bazauto/block-detection/enclosure/previews/asm_bottom.png

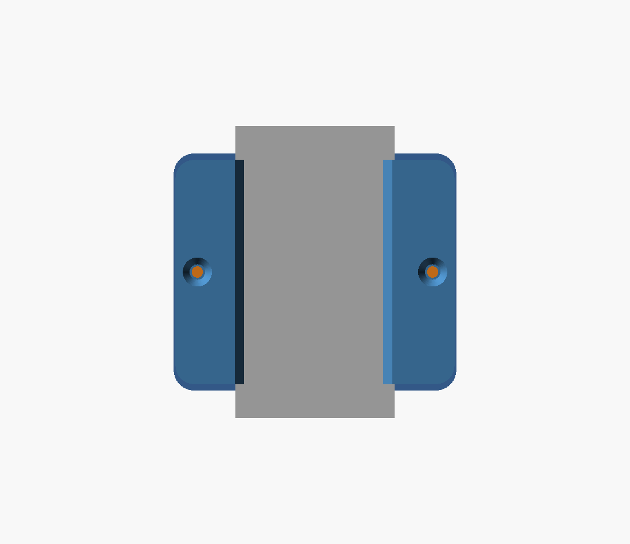
enclosure/previews/asm_bottom.png
