bazauto/block-detection/enclosure/previews/asm_front.png

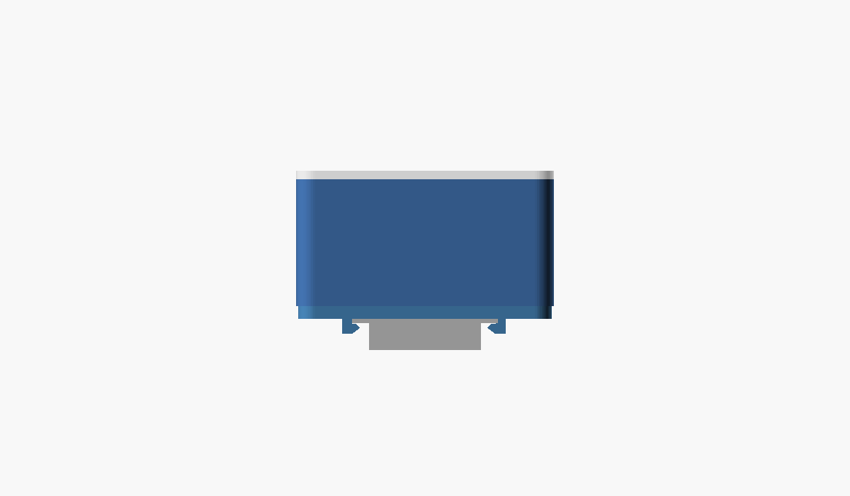
enclosure/previews/asm_front.png
