bazauto/block-detection/enclosure/previews/base_iso.png

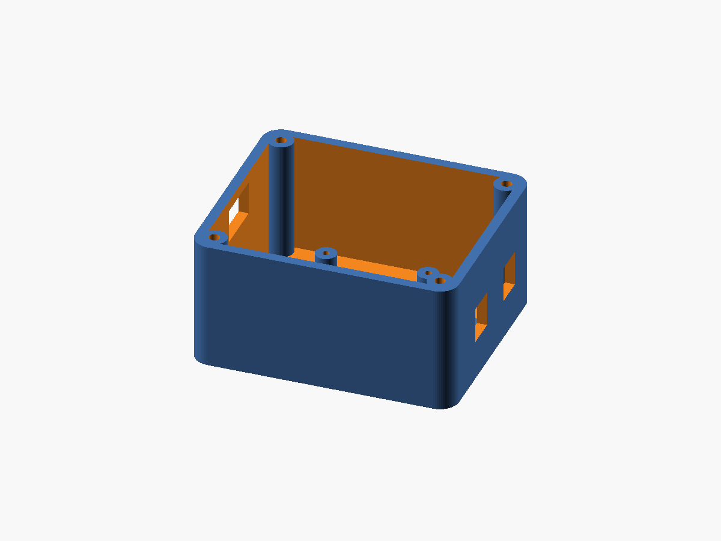
enclosure/previews/base_iso.png
