bazauto/block-detection/enclosure/previews/base_top.png

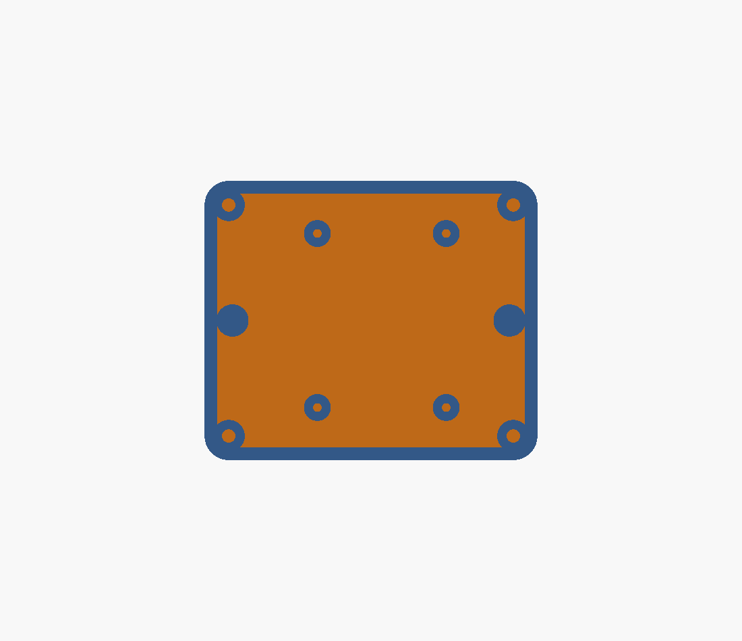
enclosure/previews/base_top.png
