bazauto/block-detection/enclosure/previews/lid_iso.png

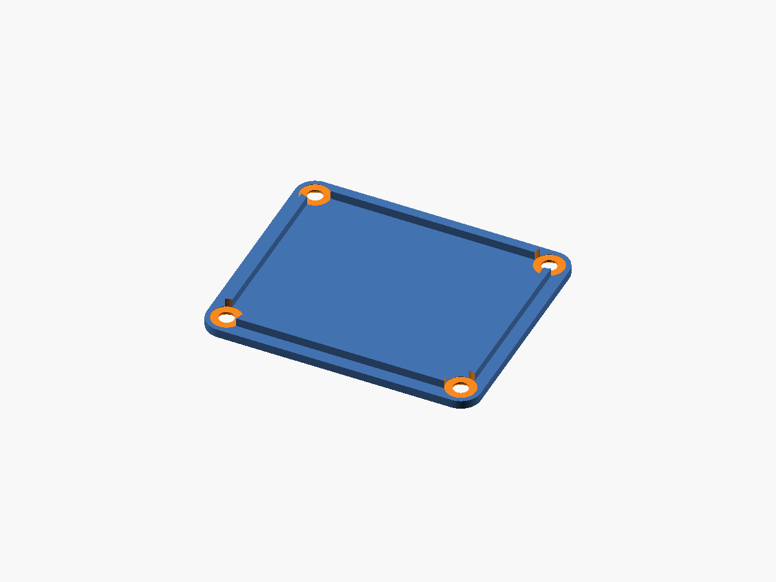
enclosure/previews/lid_iso.png
