bazauto/block-detection/enclosure/previews/sec_ct1.png

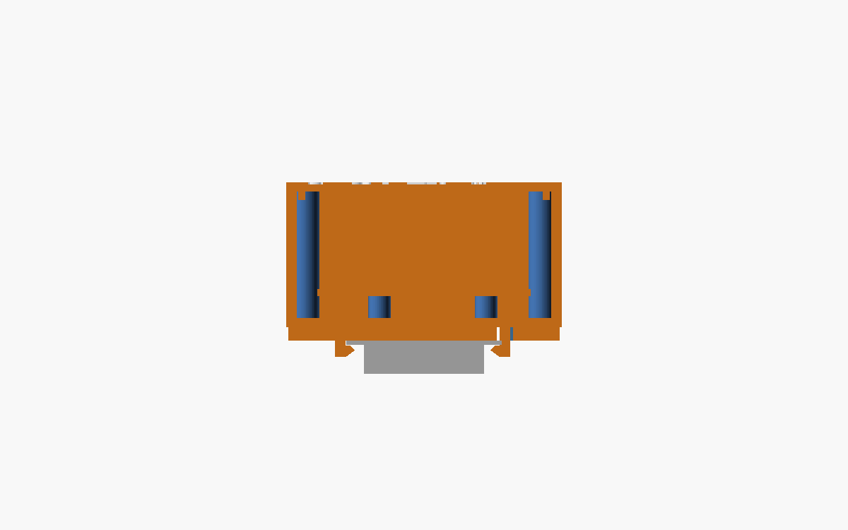
enclosure/previews/sec_ct1.png
